sje-mse/yacobo/pictures/yacobo-compare.png

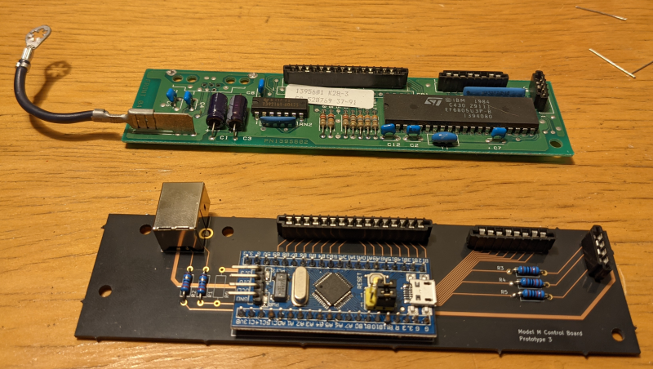
pictures/yacobo-compare.png
